LNauiz/2526_Projet2A_FlipperFlipper/Image/Batteur_onshape.png

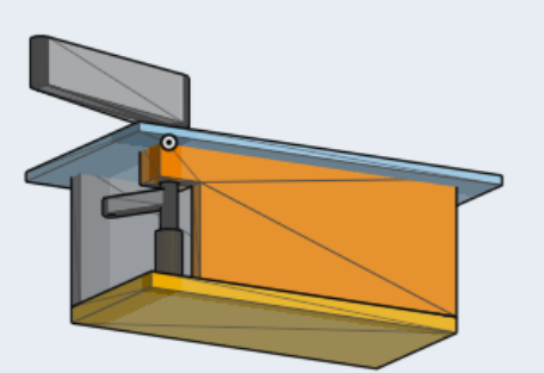
Image/Batteur_onshape.png
