LNauiz/2526_Projet2A_FlipperFlipper/Image/compteur_imprimé.png

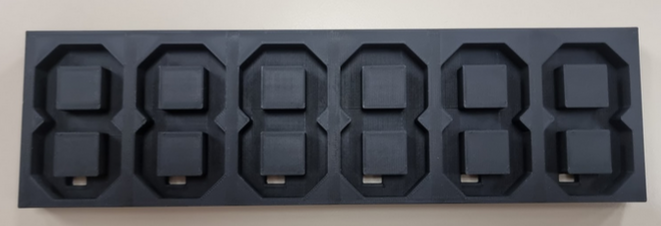
Image/compteur_imprimé.png
