LNauiz/2526_Projet2A_FlipperFlipper/Image/lanceur.jpeg

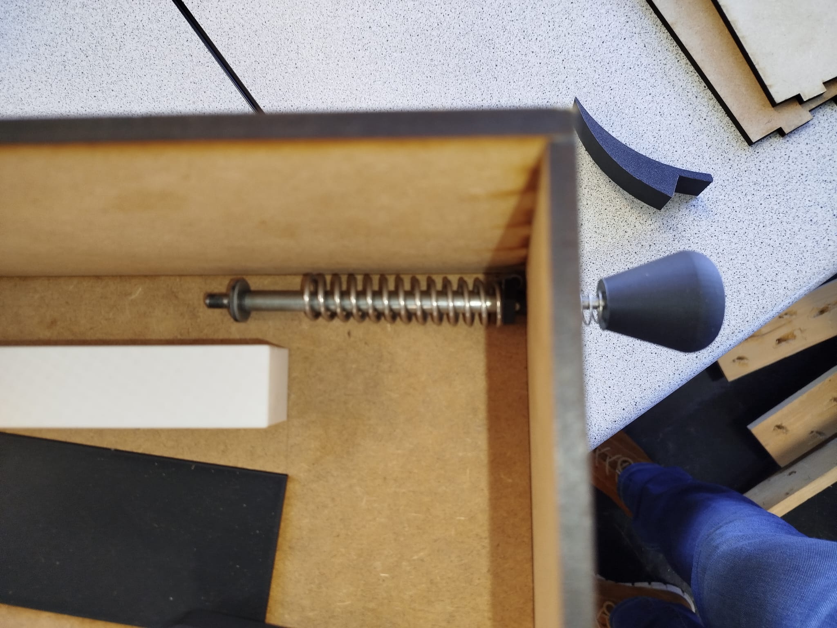
Image/lanceur.jpeg
