LNauiz/2526_Projet2A_FlipperFlipper/hardware/Modélisation 3D/Bumper/Bumper support V2.stl

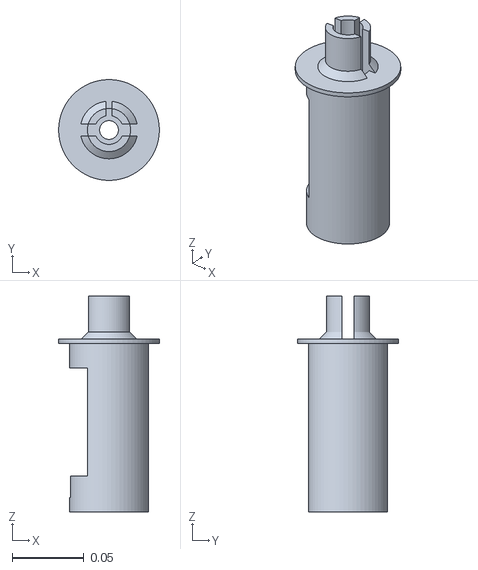
[picture p65: CAD file, 2026-03-16]
hardware/Modélisation 3D/Bumper/Bumper support V2.stl
0.07 x 0.0699 x 0.15
