LNauiz/2526_Projet2A_FlipperFlipper/hardware/Modélisation 3D/Table jeux/Imprimante 3D/Triangle obstacle.3mf

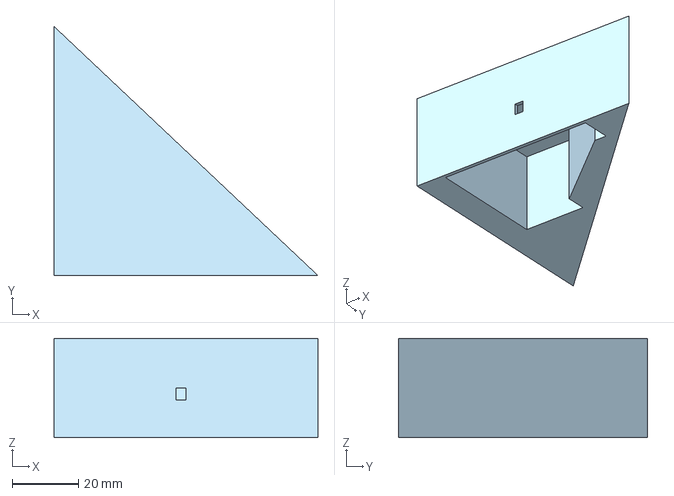
[picture p67: CAD file, 2026-03-31]
hardware/Modélisation 3D/Table jeux/Imprimante 3D/Triangle obstacle.3mf
80.0 x 75.5 x 30.0 mm
