LNauiz/2526_Projet2A_FlipperFlipper/hardware/Modélisation 3D/Batteur/Batteur bras de levier avec écrou.stl

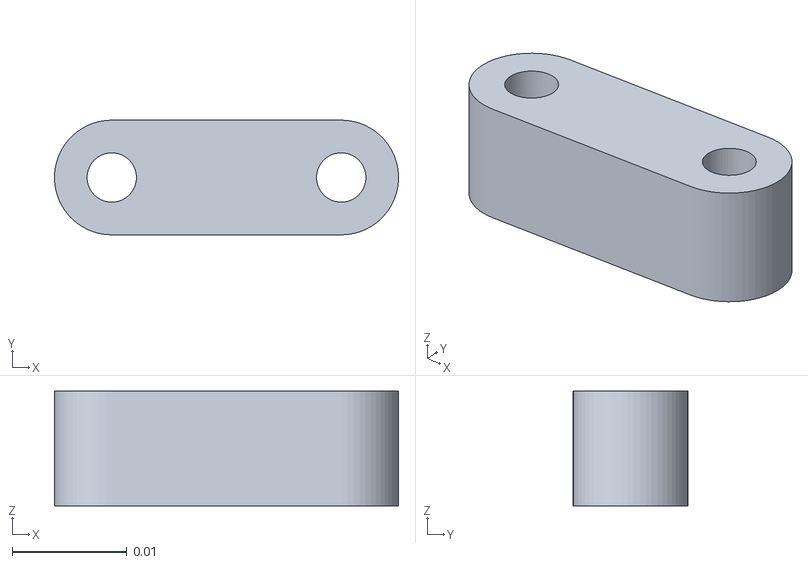
[picture p68: CAD file, 2026-03-16]
hardware/Modélisation 3D/Batteur/Batteur bras de levier avec écrou.stl
0.03 x 0.01 x 0.01
