LNauiz/2526_Projet2A_FlipperFlipper/hardware/Modélisation 3D/Bumper/Bumper support V1.3mf

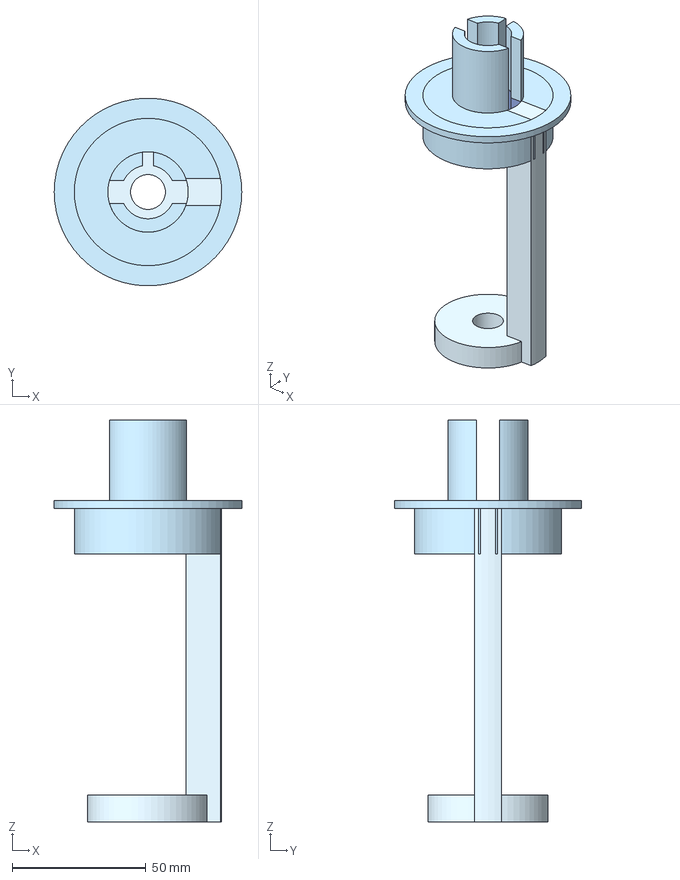
[picture p69: CAD file, 2026-03-16]
hardware/Modélisation 3D/Bumper/Bumper support V1.3mf
70.0 x 69.9 x 150.0 mm
