LNauiz/2526_Projet2A_FlipperFlipper/hardware/Modélisation 3D/Châssis/Découpeuse Laser/Châssis fond_6mm_MDF.DXF

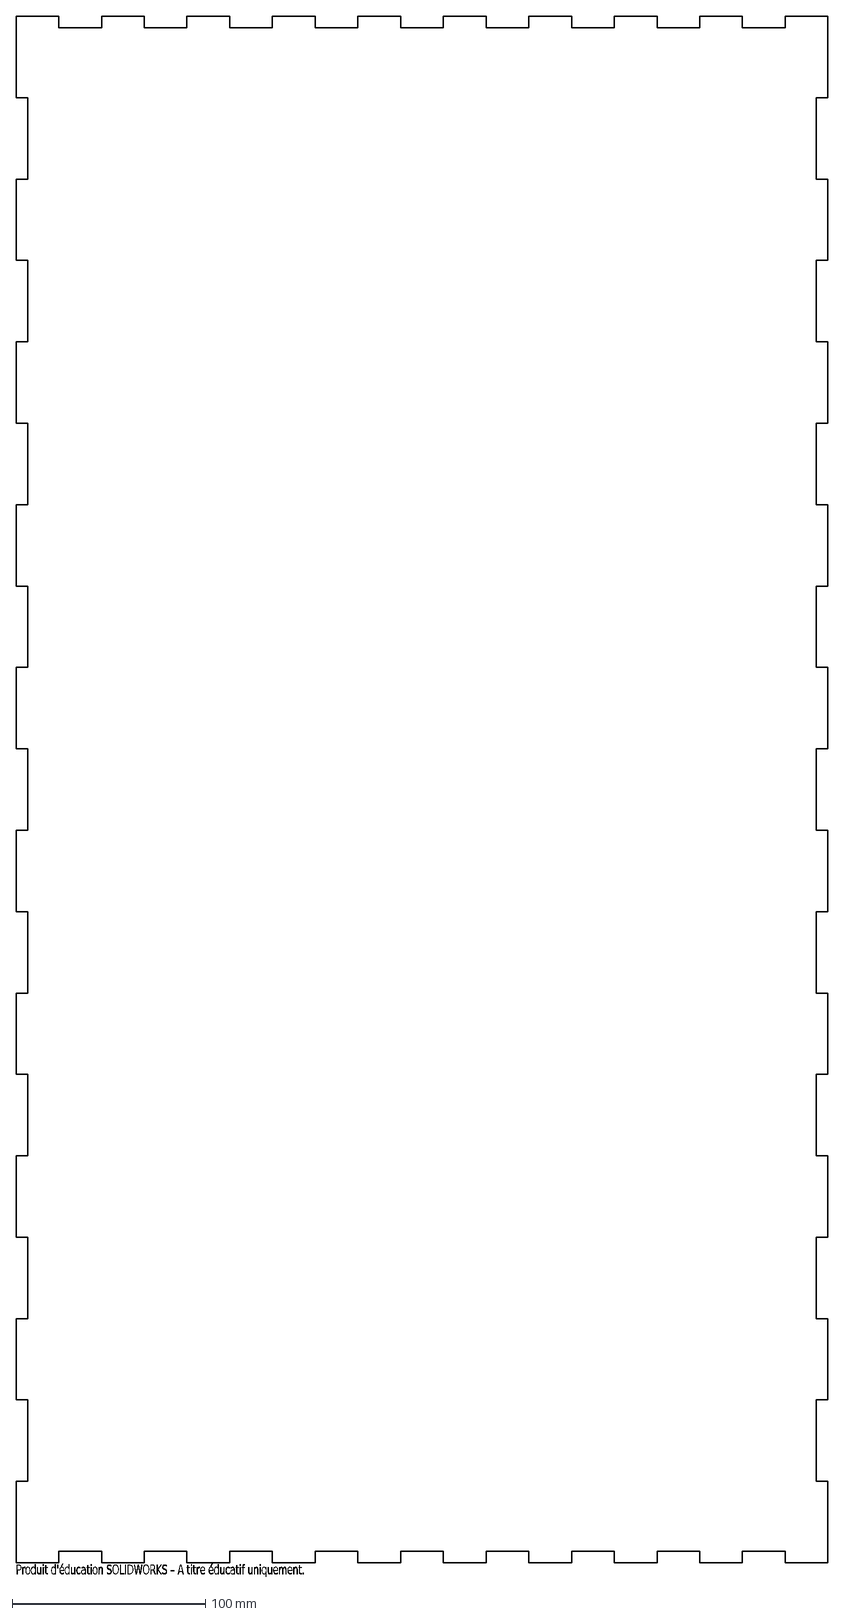
[picture p70: CAD file, 2026-03-31]
hardware/Modélisation 3D/Châssis/Découpeuse Laser/Châssis fond_6mm_MDF.DXF
Produit d'éducation SOLIDWORKS – A titre éducatif uniquement.
