LNauiz/2526_Projet2A_FlipperFlipper/hardware/Modélisation 3D/Batteur/Batteur batteur avec écrou.stl

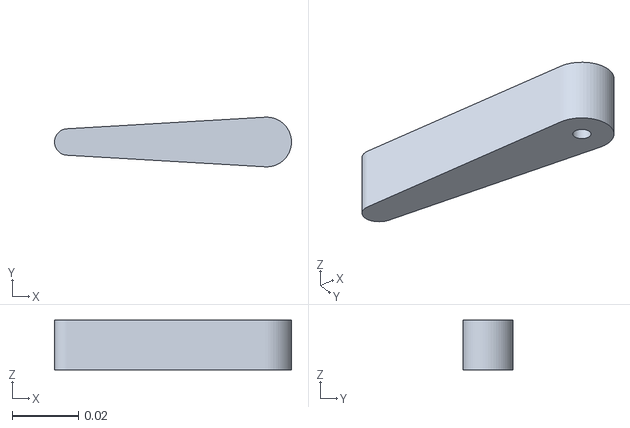
[picture p71: CAD file, 2026-03-16]
hardware/Modélisation 3D/Batteur/Batteur batteur avec écrou.stl
0.0715 x 0.015 x 0.015
