LNauiz/2526_Projet2A_FlipperFlipper/hardware/Modélisation 3D/Batteur/Batteur avec Support V2.stl

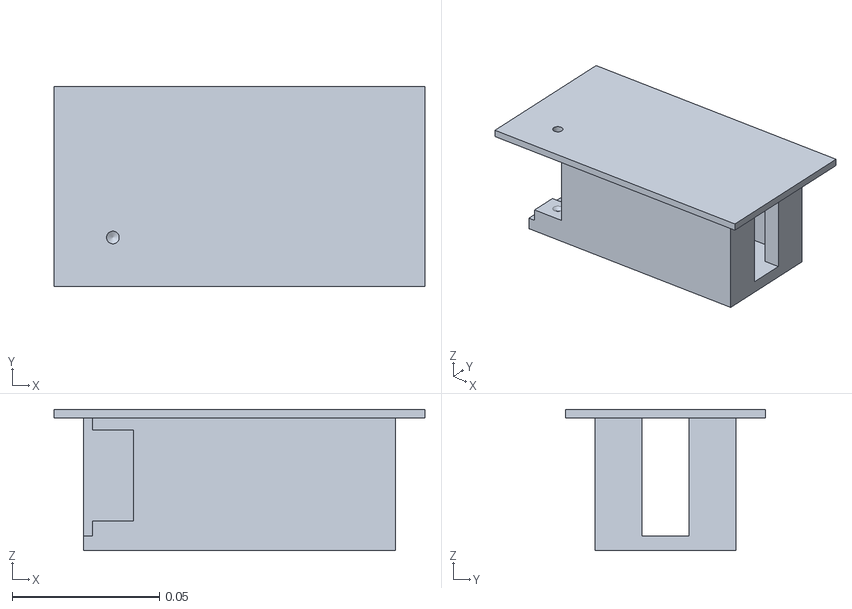
[picture p72: CAD file, 2026-03-16]
hardware/Modélisation 3D/Batteur/Batteur avec Support V2.stl
0.126 x 0.068 x 0.048
